rmingon/led-wall/wall_code/User/lookups.h

/*
 * lookups.h
 *
 *  Created on: 27 Aug 2023
 *      Author: User
 */

#ifndef USER_LOOKUPS_H_
#define USER_LOOKUPS_H_

// Define an array as a look up table for dimming to a sine pattern
u8 sine_lookup[256] = {
    0, 0, 1, 1, 2, 2, 3, 4, 6, 8, 11, 13, 15, 17, 20, 22, 25, 28, 31, 34,
    37, 40, 43, 46, 49, 53, 56, 60, 64, 67, 71, 75, 79, 83, 87, 91, 95, 99,
    103, 107, 111, 115, 119, 123, 126, 130, 133, 137, 140, 143, 146, 150, 153,
    156, 159, 162, 165, 168, 171, 174, 177, 180, 182, 185, 188, 190, 193, 195,
    198, 200, 202, 204, 206, 208, 210, 212, 214, 216, 217, 219, 220, 222, 223,
    224, 226, 227, 228, 229, 230, 231, 232, 233, 233, 234, 235, 235, 236, 236,
    237, 237, 237, 237, 237, 238, 238, 238, 238, 238, 238, 238, 238, 239, 239,
    239, 239, 239, 239, 240, 240, 240, 240, 240, 240, 240, 240, 240, 240, 240,
    240, 239, 239, 239, 239, 239, 239, 238, 238, 238, 238, 238, 238, 238, 238,
    238, 237, 237, 237, 237, 237, 236, 236, 235, 235, 234, 233, 233, 232, 231,
    230, 229, 228, 227, 226, 224, 223, 222, 220, 219, 217, 216, 214, 212, 210,
    208, 206, 204, 202, 200, 198, 195, 193, 190, 188, 185, 182, 180, 177, 174,
    171, 168, 165, 162, 159, 156, 153, 150, 146, 143, 140, 137, 133, 130, 126,
    123, 119, 115, 111, 107, 103, 99, 95, 91, 87, 83, 79, 75, 71, 67, 64, 60,
    56, 53, 49, 46, 43, 40, 37, 34, 31, 28, 25, 22, 20, 17, 15, 13, 11, 8, 6,
    4, 3, 2, 2, 1, 1, 0, 0
};

// "Sine" Wave lookup table
const u8 sine_lookup_2[256] = {
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
  91, 48, 0, 255, 255, 139, 16, 76, 32, 89, 45, 13, 0, 32, 97, 234,
  78, 154, 45, 236, 142, 235, 73, 236, 226, 50, 167, 201, 93, 50, 181, 145,
  24, 3, 72, 52, 15, 44, 134, 0, 0, 255, 57, 255, 20, 255, 5, 0,
  26, 10, 0, 31, 219, 0, 0, 70, 71, 0, 31,
};

#endif /* USER_LOOKUPS_H_ */
